BlathanAevon/ESP32_TOTP/src/sprites.h

#include <Arduino.h>

static const unsigned char PROGMEM image_hour_glass[] = {
  0xff, 0xff, 0xff, 0xff, 0x80, 0xff, 0xff, 0xff, 0xff, 0x80, 0xff, 0xff, 0xff,
  0xff, 0x80, 0x1c, 0x00, 0x00, 0x1c, 0x00, 0x1c, 0x00, 0x00, 0x1c, 0x00, 0x1c,
  0x00, 0x00, 0x1c, 0x00, 0x1c, 0x00, 0x00, 0x1c, 0x00, 0x1c, 0x00, 0x00, 0x1c,
  0x00, 0x1c, 0x00, 0x00, 0x1c, 0x00, 0x1c, 0x70, 0x07, 0x1c, 0x00, 0x1c, 0x70,
  0x07, 0x1c, 0x00, 0x1c, 0x70, 0x07, 0x1c, 0x00, 0x1c, 0x7f, 0xff, 0x1c, 0x00,
  0x1c, 0x7f, 0xff, 0x1c, 0x00, 0x1c, 0x7f, 0xff, 0x1c, 0x00, 0x03, 0x8f, 0xf8,
  0xe0, 0x00, 0x03, 0x8f, 0xf8, 0xe0, 0x00, 0x03, 0x8f, 0xf8, 0xe0, 0x00, 0x00,
  0x71, 0xc7, 0x00, 0x00, 0x00, 0x71, 0xc7, 0x00, 0x00, 0x00, 0x71, 0xc7, 0x00,
  0x00, 0x00, 0x0e, 0x38, 0x00, 0x00, 0x00, 0x0e, 0x38, 0x00, 0x00, 0x00, 0x0e,
  0x38, 0x00, 0x00, 0x00, 0x0e, 0x38, 0x00, 0x00, 0x00, 0x0e, 0x38, 0x00, 0x00,
  0x00, 0x0e, 0x38, 0x00, 0x00, 0x00, 0x70, 0x07, 0x00, 0x00, 0x00, 0x70, 0x07,
  0x00, 0x00, 0x00, 0x70, 0x07, 0x00, 0x00, 0x03, 0x81, 0xc0, 0xe0, 0x00, 0x03,
  0x81, 0xc0, 0xe0, 0x00, 0x03, 0x81, 0xc0, 0xe0, 0x00, 0x1c, 0x01, 0xc0, 0x1c,
  0x00, 0x1c, 0x01, 0xc0, 0x1c, 0x00, 0x1c, 0x01, 0xc0, 0x1c, 0x00, 0x1c, 0x0f,
  0xf8, 0x1c, 0x00, 0x1c, 0x0f, 0xf8, 0x1c, 0x00, 0x1c, 0x0f, 0xf8, 0x1c, 0x00,
  0x1c, 0x7f, 0xff, 0x1c, 0x00, 0x1c, 0x7f, 0xff, 0x1c, 0x00, 0x1c, 0x7f, 0xff,
  0x1c, 0x00, 0x1f, 0xff, 0xff, 0xfc, 0x00, 0x1f, 0xff, 0xff, 0xfc, 0x00, 0x1f,
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
  0x03, 0x80, 0x00, 0x03, 0x80, 0x03, 0x80, 0x00, 0x03, 0x80, 0x03, 0x80, 0x00,
  0x03, 0x80, 0x00, 0x7f, 0xff, 0xfc, 0x00, 0x00, 0x7f, 0xff, 0xfc, 0x00, 0x00,
  0x7f, 0xff, 0xfc, 0x00, 0x00, 0x00, 0x00, 0x00, 0x00, 0x00, 0x00, 0x00, 0x00,
  0x00, 0x00, 0x00, 0x00, 0x00, 0x00
};
